Venomous-pie/BIOMETRICSMANPRO/crowpanel_firmware/src/core/certs.h

#pragma once

// GTS Root R4 — Google Trust Services root CA
// Valid until 2036-06-22. Used to verify demo.manpromanagement.com via WE1 intermediate.
// Store in PROGMEM to avoid consuming RAM on the CrowPanel S3.
static const char GTS_ROOT_R4[] PROGMEM = R"EOF(
-----BEGIN CERTIFICATE-----
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
-----END CERTIFICATE-----
)EOF";
