Venomous-pie/BIOMETRICSMANPRO/crowpanel_firmware/src/core/comm_manager.h

#ifndef COMM_MANAGER_H
#define COMM_MANAGER_H

#include <Arduino.h>
#include <esp_now.h>

// ============================================================
// ESP-NOW configuration  (Option A — fixed channel)
// Must match ESPNOW_CHANNEL and WROOM_MAC on the WROOM side.
// ============================================================
#define ESPNOW_CHANNEL 1   // Must match your router's fixed channel
#define API_BASE_URL   "https://demo.manpromanagement.com"  // Change to mock server IP for local dev

// The WROOM's station MAC address.
// PLACEHOLDER: Flash the WROOM first and read its "[BOOT] WROOM MAC:" line,
// then paste those 6 hex bytes here before flashing the CrowPanel.
static const uint8_t WROOM_MAC[6] = {0x30, 0x76, 0xF5, 0x90, 0x6A, 0xEC}; // 30:76:f5:90:6a:ec

class CommManager {
public:
    static void begin();    // Inits ESP-NOW, registers callbacks, adds WROOM as peer
    static void process();  // Call from loop() — drains ring buffer, dispatches JSON
    static void sendCommand(const String& cmd);
    static void sendDebug(const String& msg);
    static void sendSyncPacket(const uint8_t* payload, size_t len);

    // ESP-NOW receive callback — runs in WiFi task (Core 0).
    // Copies payload into the ring buffer; all parsing is done in process().
    // Arduino Core 3.x (IDF 5.x): recv callback takes esp_now_recv_info_t* not uint8_t* mac
    static void onEspNowRecv(const esp_now_recv_info_t* recv_info, const uint8_t* data, int len);

private:
    static void dispatchJson(const String& line);
    static String serialBuf; // USB Serial forwarder accumulator
};

#endif // COMM_MANAGER_H
