Venomous-pie/BIOMETRICSMANPRO/crowpanel_firmware/src/ui/ui_enroll.h

#ifndef UI_ENROLL_H
#define UI_ENROLL_H

#include <Arduino.h>
#include <lvgl.h>
#include "../core/data_manager.h"

extern lv_obj_t *scr_enroll;
extern lv_obj_t *scr_choose_finger;
void buildEnrollScreen();
void buildEmpListScreen();
void buildChooseFingerScreen();
void uiShowEmpList(bool isFallback = false);
void uiShowChooseFinger(String emp_id, const char *name, const char *dept, bool isFallback = false);
void uiShowEnrollStart(const char *name);
void uiShowEnrollStep(int step, const char *msg);
void uiShowEnrollResult(bool ok, const char *name);
void cleanupEnrollScreens();
#endif // UI_ENROLL_H
