Venomous-pie/BIOMETRICSMANPRO/crowpanel_firmware/src/ui/ui_result.h

#ifndef UI_RESULT_H
#define UI_RESULT_H

#include <lvgl.h>

void buildResultScreen();
void uiShowMatch(const char *name, const char *dept, const char *action, const char *ts);
void uiShowNoMatch();
void uiShowActionDenied(const char *name, uint8_t action_type);

#endif // UI_RESULT_H
